tonykoop/sambuca/capstone-deck.pptx

Sambuca

A modern boat-shaped arched harp
inspired by the Royal Cemetery of Ur, c. 2600 BC
SAM-13-ROOT prototype + parametric family of five variants

Tony Koop · Heifer Zephyr · Fall 2026 capstone

## Slide 2

Where this instrument comes from

And what that gives us.

The artifact

- BM 121198, Royal Cemetery at Ur, c. 2600 BC.
- British Museum curator's card: "more accurately described as a boat-shaped harp" — not a lyre.
- Surviving Sumerian material: gold tuning pegs and lapis lazuli decorations. The wood is a 1971–72 reconstruction.

What that means

- The visual fingerprint is locked.
- Everything underneath is design freedom.
- Inspired by the Sumerian pattern — not a reproduction of any specific artifact, not a claim against any modern living tradition.

Sambuca · Fall 2026 capstone · private review

## Slide 3

Fingerprint preservation

Eight elements that read as Sumerian sambuca.

- Gold-flared cap at the neck top.
- 13 bulb-headed tuning pegs with visible cord wraps.
- Strong J-curve neck.
- Multi-strip lapis band along the soundboard-hull seam.

- Brass collar at the neck-body joint.
- Slim boat hull with pronounced bow lift.
- Rectangular pale inlay panel at the bow end.
- Two integral stub blocks at the stern keel.

Sambuca · Fall 2026 capstone · private review

## Slide 4

What I'm modernizing

Where the build departs from the pattern.

- Soundhole at the keel, not the soundboard — projects sound away from the player toward the listener.
- Geared guitar tuners hidden inside the neck, behind PVD-gold-tone bulb caps and decorative cord wraps.
- Modern strings — fluorocarbon trebles + wound nylon basses, 65–80 kgf calibrated total.
- CNC fabrication for the hull, neck, inlay, and stand.
- Japanese kanawa-tsugi joinery on the stand — a stylistic choice, not Sumerian.

Sambuca · Fall 2026 capstone · private review

## Slide 5

Family spec

One MasterLayout, five buildable variants.

ID | Body length | Strings | Tuning range | Harness | Role
SAM-13-ROOT | 650 mm | 13 | G3 → E5 | none | build target
SAM-19-MID | 850 mm | 19 | D3 → G5 | low-back belt | mid concert
SAM-25-CONCERT | 1050 mm | 25 | A2 → A5 | sax harness | concert
SAM-13-AE | 650 mm | 13 | G3 → E5 | none | acoustic-electric
SAM-13-MULE | 650 mm | 13 | G3 → E5 (reduced T) | none | tension test mule

All five share one parametric MasterLayout. body_length_mm and string_count drive the configurations.

Sambuca · Fall 2026 capstone · private review

## Slide 6

Parametric SolidWorks workflow

One equations file, one design table, five buildable instruments.

Sources of truth

- cad/SAM-000_master-equations.txt — global equations.
- SolidWorks Equations Manager binds every dimension by name.
- Design table drives 5 configurations from 4 anchor parameters.

Driving parameters

- body_length_mm (650 / 850 / 1050)
- string_count (13 / 19 / 25)
- f_min_hz, f_max_hz (tuning anchors)
- scale_factor derives the rest

Sambuca · Fall 2026 capstone · private review

## Slide 7

Acoustic study results

Predicting and validating the voice.

What Wolfram predicts

- 3.8 L hull cavity — small.
- Keel-port Helmholtz: ~143 Hz.
- First plate mode (cedar @ 3 mm): ~160 Hz.
- Coupled cavity-plate pair: ~125 Hz / ~185 Hz.
- Bass strings sit just above the lower coupled mode — the voicing sweet spot.

How we'll validate

- Sweep frequency response on the SAM-13-MULE.
- SPL measurement at 1 m with calibrated mic.
- Tolerance: predicted ±6 dB.
- Escalation paths: thinner cedar, larger port, or pickup configuration.

Sambuca · Fall 2026 capstone · private review

## Slide 8

Inlay program

Multi-strip lapis band + bow inlay panel, all CNC-driven.

- Multi-strip lapis band: 5 parallel strips × 1.5 mm dyed-blue veneer with 0.8 mm light spacers (~12 mm total band width).
- Single-pass CNC route with a 0.8 mm end mill — same setup as the bow-panel pocket.
- Bow-end inlay panel: 100 × 60 mm pale rectangular panel framing the string-anchor zone (mother-of-pearl or shell composite).
- Inlay program is parametric — scales with scale_factor for SAM-19 and SAM-25.
- Brand integration (Heifer Zephyr wordmark) is added in a separate inlay pass once Option A (soundboard) or Option B (stand) is locked.

Sambuca · Fall 2026 capstone · private review

## Slide 9

Build sequence

12 stages, 60–90 hours of active build time over 6–10 weeks.

Stages

- Stage 1: hull (CNC-from-block or stave-laminated).
- Stage 2: neck (3-laminate sapele, CNC sweep).
- Stage 3: soundboard with inlay pockets.
- Stage 4: scarf joint + brass collar.
- Stage 5: soundboard installation + inlay.

Hold points

- Stage 9: string-holder strip voicing on the MULE.
- Stage 10a: 30-day MULE tension hold — public-release gate.
- Stage 10b: SAM-13-ROOT gradual stringing to 65–80 kgf.
- Stage 11: acoustic measurement vs prediction.

Sambuca · Fall 2026 capstone · private review

## Slide 10

Validation gates

Three blockers between private review and public release.

- Structural — SAM-13-MULE 30-day neck-deflection hold under reduced tension. Pass criterion: ≤2 mm deflection at the gold cap.
- Cultural — advisor review of the provenance language. Sumerian pattern is public domain; the sambykē etymological link is honestly flagged as historically contested.
- Brand — Heifer Zephyr wordmark placement option (A soundboard vs B stand) locked.

Sambuca · Fall 2026 capstone · private review

## Slide 11

Cultural provenance language

The public-release standard, locked.

- Inspired by the Sumerian pattern (~4500 years old, public domain).
- Not a reproduction of any specific surviving artifact.
- Not a recreation of any reconstructed instrument such as BM 121198.
- Not a claim of cultural authority over any modern living tradition.
- Sambykē (σαμβύκη) etymological link to the Sumerian form is historically contested. This build adopts "sambuca" while acknowledging the uncertainty.

Sambuca · Fall 2026 capstone · private review

## Slide 12

Finished prototype

SAM-13-ROOT, finished, tuned, played.

[HERO-01 — SAM-13-ROOT three-quarter on stand, soft directional light]

"Acoustic harp inspired by a pattern 4500 years older than this room, built with CNC and tuned for the room you'd play it in."

Sambuca · Fall 2026 capstone · private review

## Slide 13

What I learned

Three honest takeaways.

- The string-holder strip belongs in arched-harp practice; the "bridge bar" was a kora-pattern leak that almost cost me a wrong build. Reverse-engineering happened in real time during this packet build.
- Coupled cavity-plate analysis predicts voice more accurately for arched harps than the single-cavity model I started with.
- "Fingerprint preservation, modernize everything else" framing scales. It works for the sambuca, and would work for any pattern instrument with surviving fragments + interpretive wood.

Sambuca · Fall 2026 capstone · private review

## Slide 14

What's next

The roadmap from prototype to release.

Before release

- Cultural advisor review (in progress).
- SAM-13-MULE build for tension validation.
- Brand integration option locked.

Then

- Public release with site/index.html + GitHub repo + capstone showing.
- SAM-19-MID and SAM-25-CONCERT queued for 2027.
- Learn-to-play songbook (paired with the sheet-music skill).

Sambuca · Fall 2026 capstone · private review

## Slide 15

Credits & sources

Where this came from, who's owed credit.

- British Museum object 121198 — © Trustees of the British Museum, CC BY-NC-SA 4.0. Photos by Don Hitchcock, 2015.
- Herbology Manchester supplemental profile photo.
- Penn Museum object 47880 / B16728 — courtesy Penn Museum, University of Pennsylvania.
- Kora MasterLayout as parametric template (C:\Users\Tony\Documents\GitHub\kora).
- Heifer Zephyr workshop, Maker Nexus shop access.
- Tony Koop, with the instrument-maker-v4 skill from Anthropic.

Sambuca · Fall 2026 capstone · private review
